Tonikiller10000/8BitProcessor/ClkPulseGenerator/ComputerClk_Pictures/20220915_213736.jpg

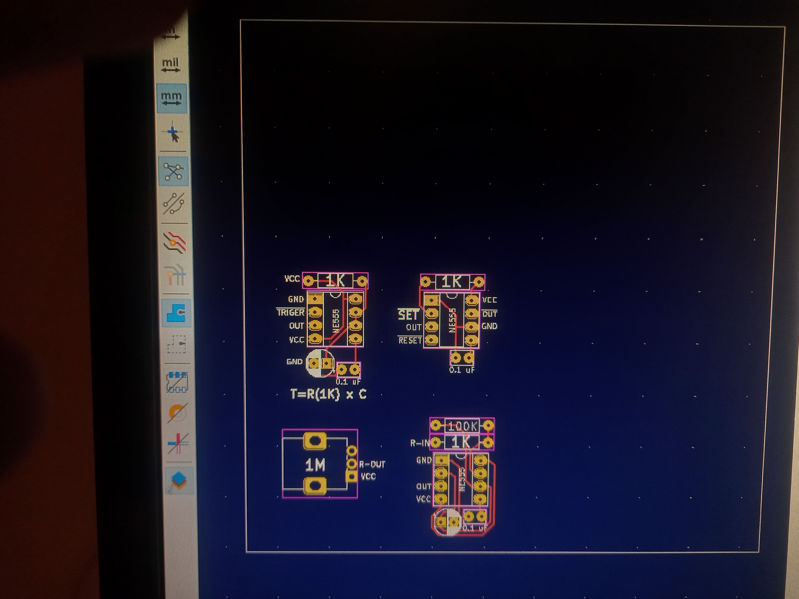
ClkPulseGenerator/ComputerClk_Pictures/20220915_213736.jpg
