Tonikiller10000/8BitProcessor/ClkPulseGenerator/ComputerClk_Pictures/20221016_185711.jpg

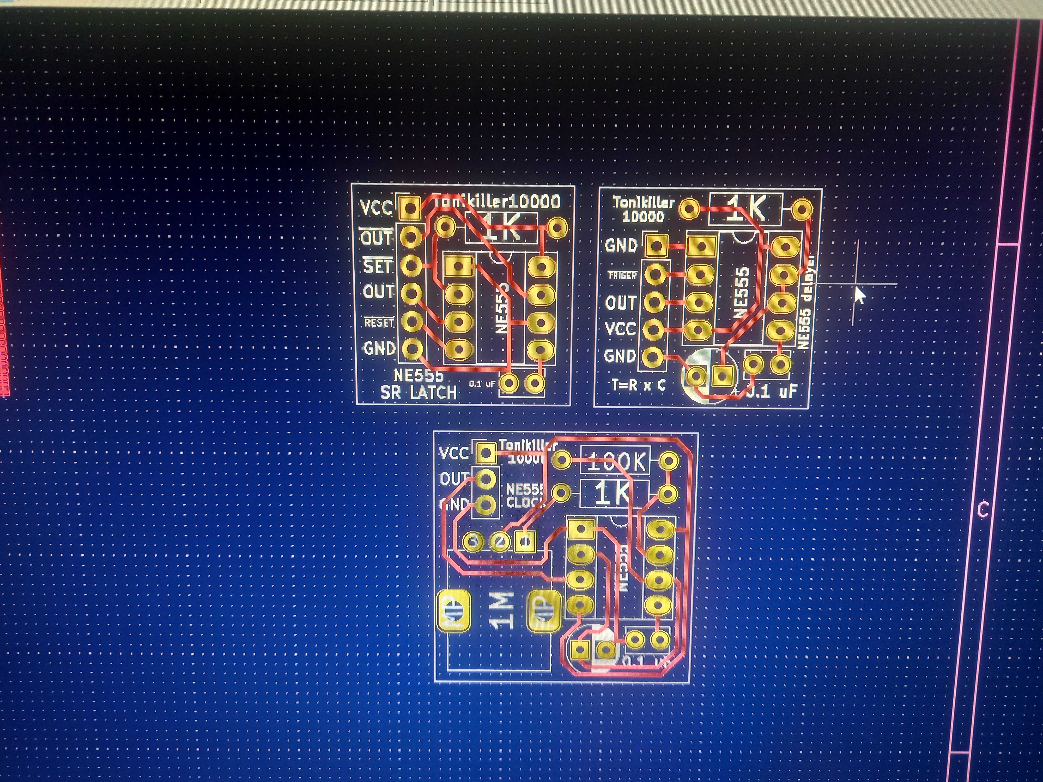
ClkPulseGenerator/ComputerClk_Pictures/20221016_185711.jpg
