Tonikiller10000/8BitProcessor/ClkPulseGenerator/ComputerClk_Pictures/20221231_235716.jpg

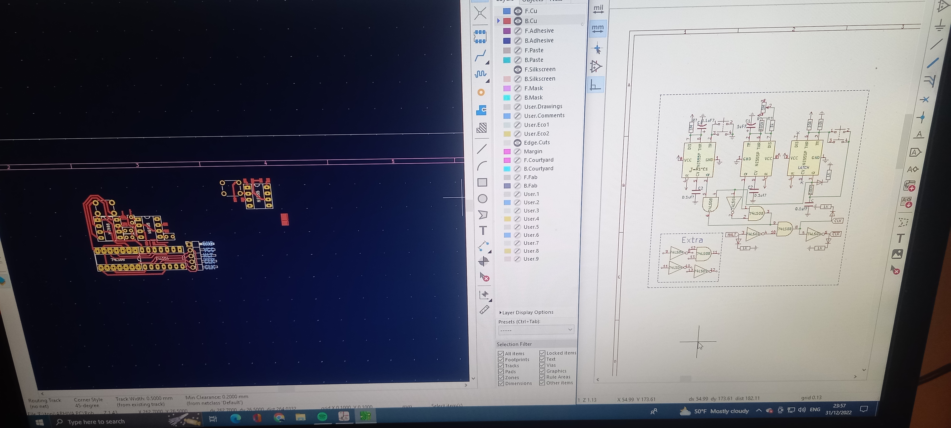
ClkPulseGenerator/ComputerClk_Pictures/20221231_235716.jpg
