Tonikiller10000/8BitProcessor/ClkPulseGenerator/ComputerClk_Pictures/20230512_194840.jpg

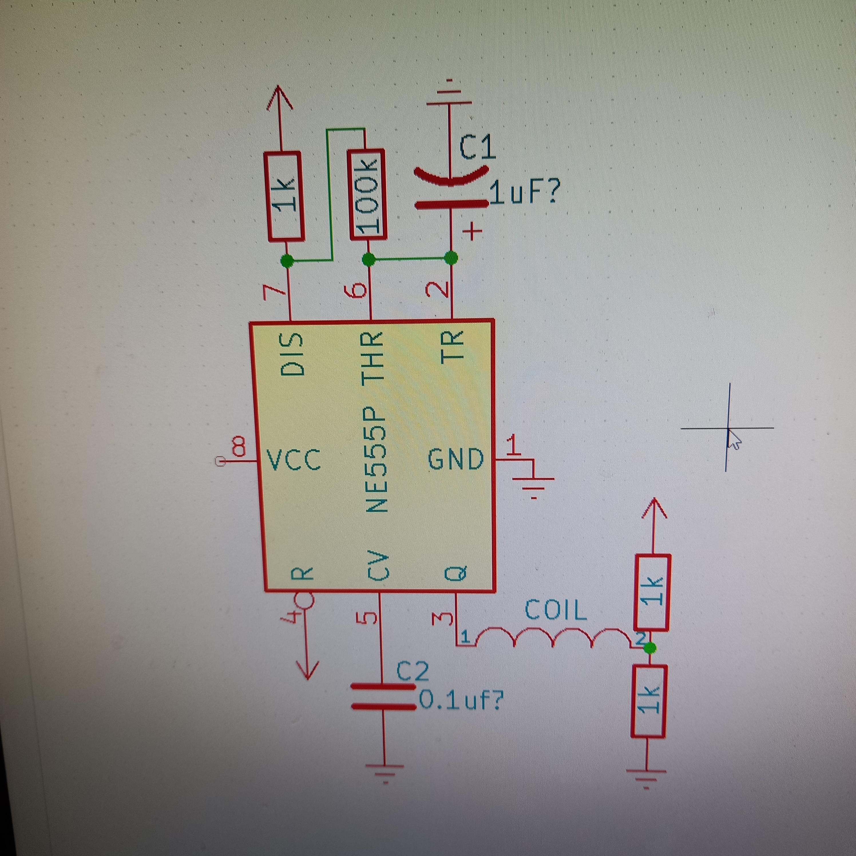
ClkPulseGenerator/ComputerClk_Pictures/20230512_194840.jpg
