Tonikiller10000/8BitProcessor/ClkPulseGenerator/ComputerClk_Pictures/20230818_153651.jpg

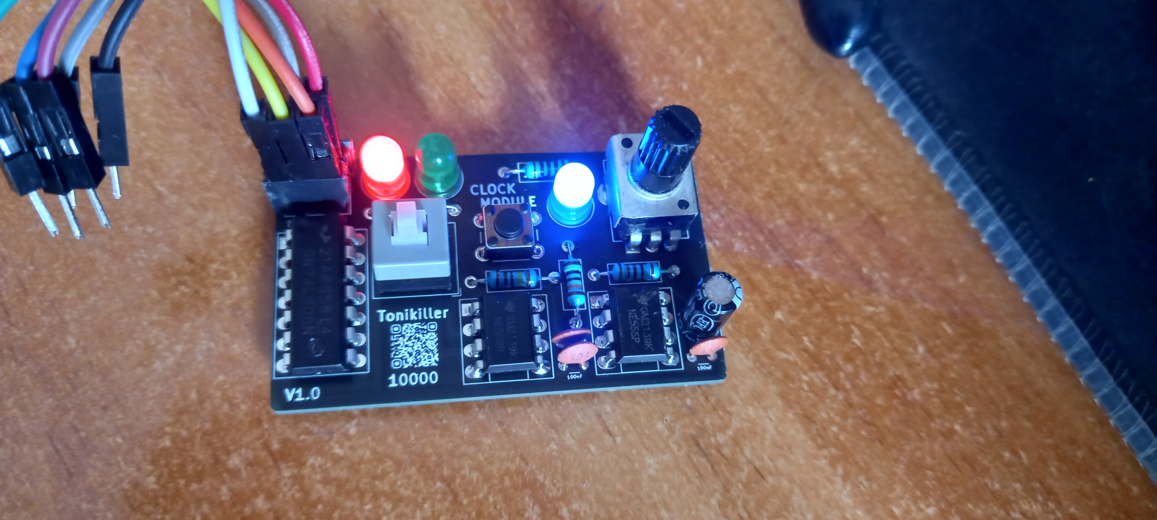
ClkPulseGenerator/ComputerClk_Pictures/20230818_153651.jpg
