Tonikiller10000/8BitProcessor/ClkPulseGenerator/ComputerClk_Pictures/p1.jpg

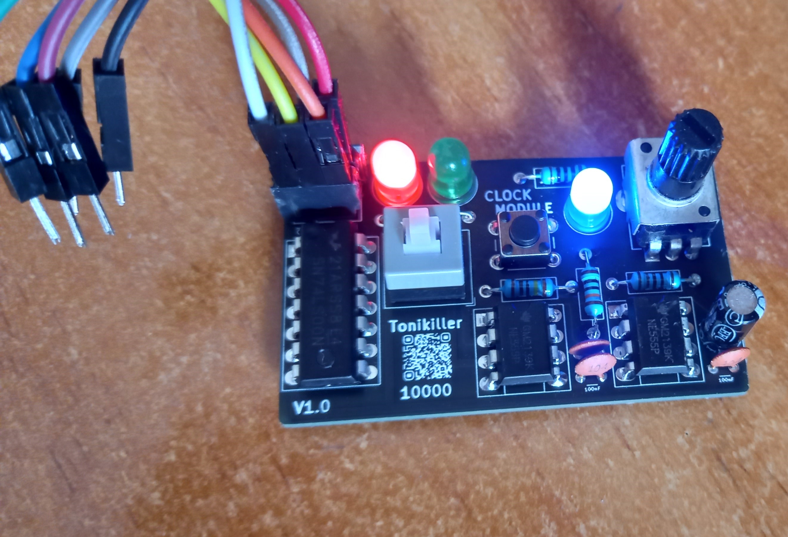
ClkPulseGenerator/ComputerClk_Pictures/p1.jpg
