Tonikiller10000/8BitProcessor/ClkPulseGenerator/ComputerClk_Pictures/p2.jpg

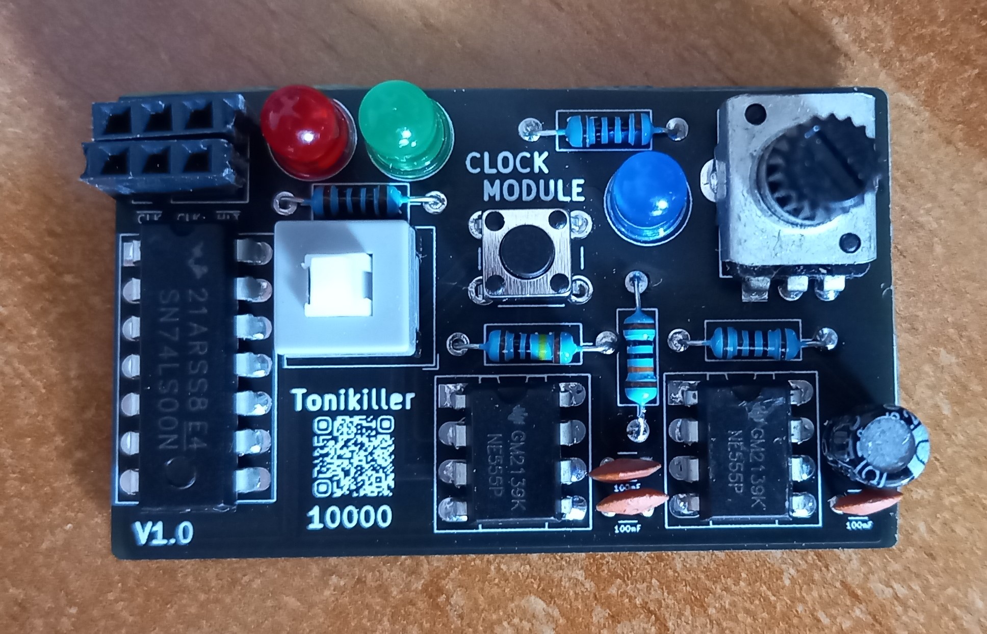
ClkPulseGenerator/ComputerClk_Pictures/p2.jpg
