Tonikiller10000/8BitProcessor/ClkPulseGenerator/ComputerClk_Pictures/s1.png

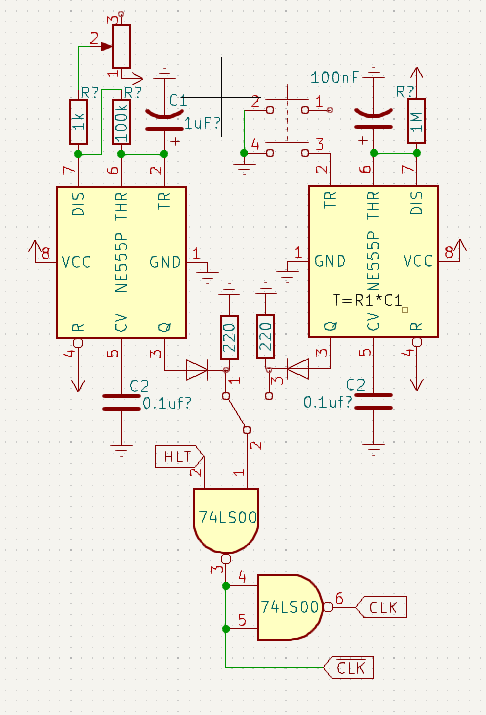
ClkPulseGenerator/ComputerClk_Pictures/s1.png
