Tonikiller10000/8BitProcessor/ClkPulseGenerator/ComputerClk_Pictures/s2.png

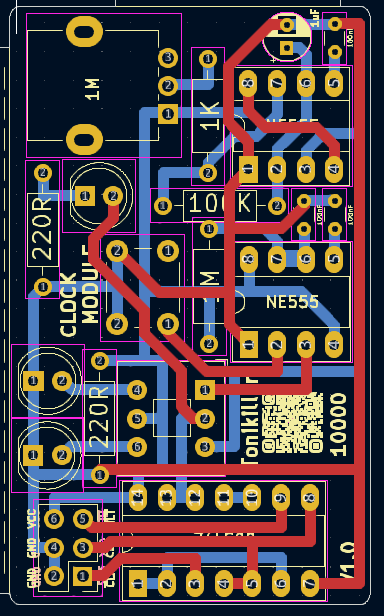
ClkPulseGenerator/ComputerClk_Pictures/s2.png
