Tonikiller10000/8BitProcessor/ClkPulseGenerator/ComputerClk_Pictures/s3.png

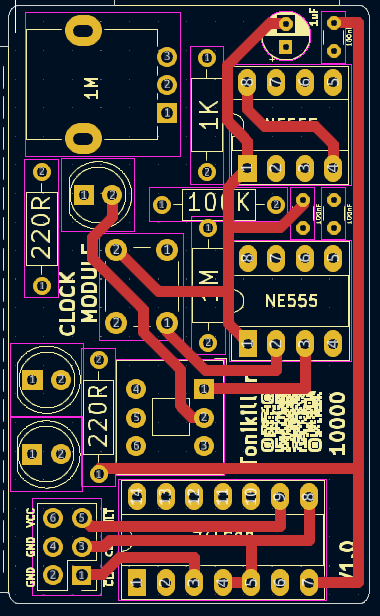
ClkPulseGenerator/ComputerClk_Pictures/s3.png
