Tonikiller10000/8BitProcessor/ClkPulseGenerator/ComputerClk_Pictures/Screenshot 2023-10-15 125649.png

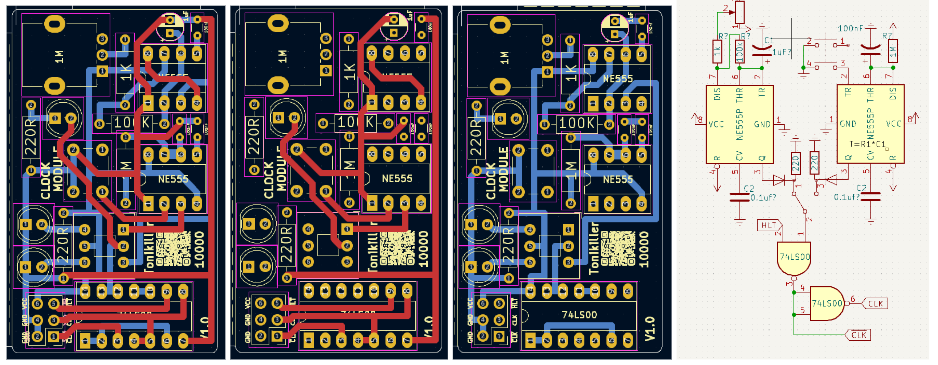
ClkPulseGenerator/ComputerClk_Pictures/Screenshot 2023-10-15 125649.png
