Tonikiller10000/8BitProcessor/ClkPulseGenerator/ComputerClk_Pictures/{35175EC8-5557-4C38-9353-143CC6CB5B68}.png

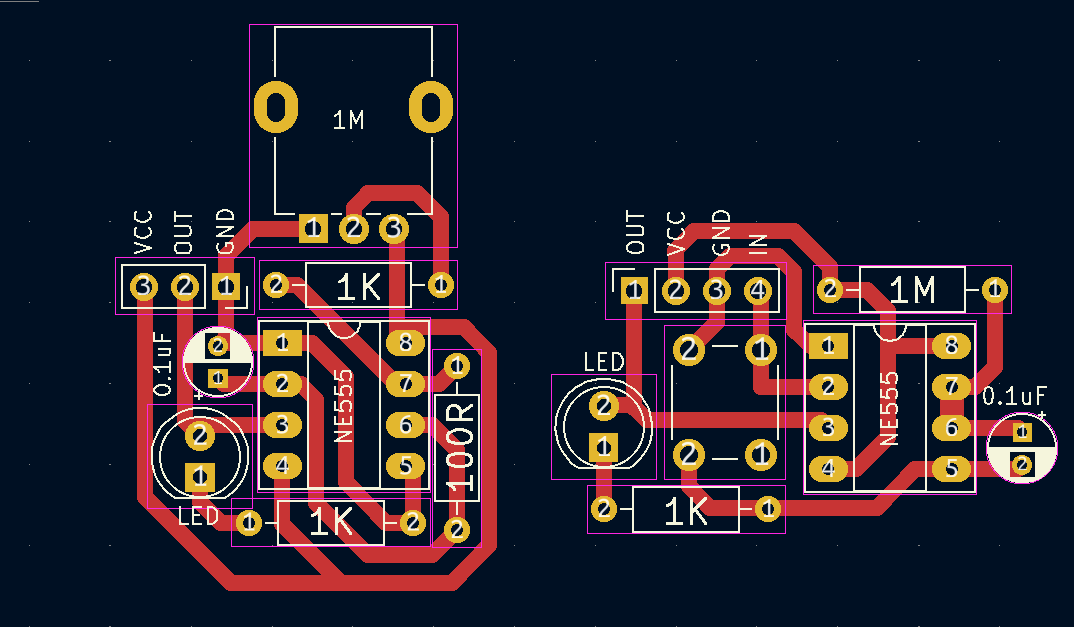
ClkPulseGenerator/ComputerClk_Pictures/{35175EC8-5557-4C38-9353-143CC6CB5B68}.png
