Tonikiller10000/8BitProcessor/DisplayRegister/DisplayRegister_Pictures/DisplayRegisterPicture (1).jpg

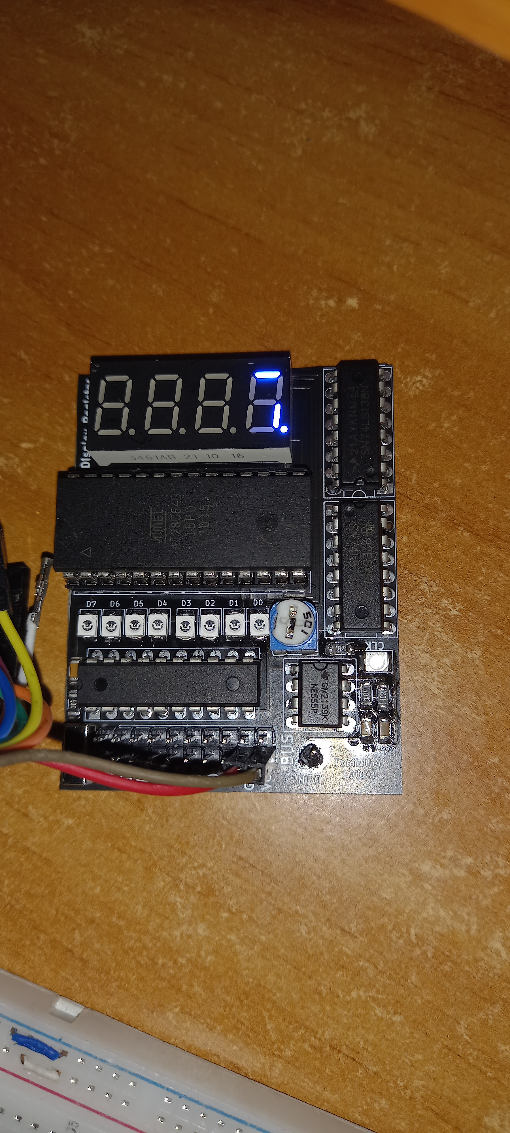
DisplayRegister/DisplayRegister_Pictures/DisplayRegisterPicture (1).jpg
