Tonikiller10000/8BitProcessor/DisplayRegister/DisplayRegister_Pictures/DisplayRegisterPicture (2).jpg

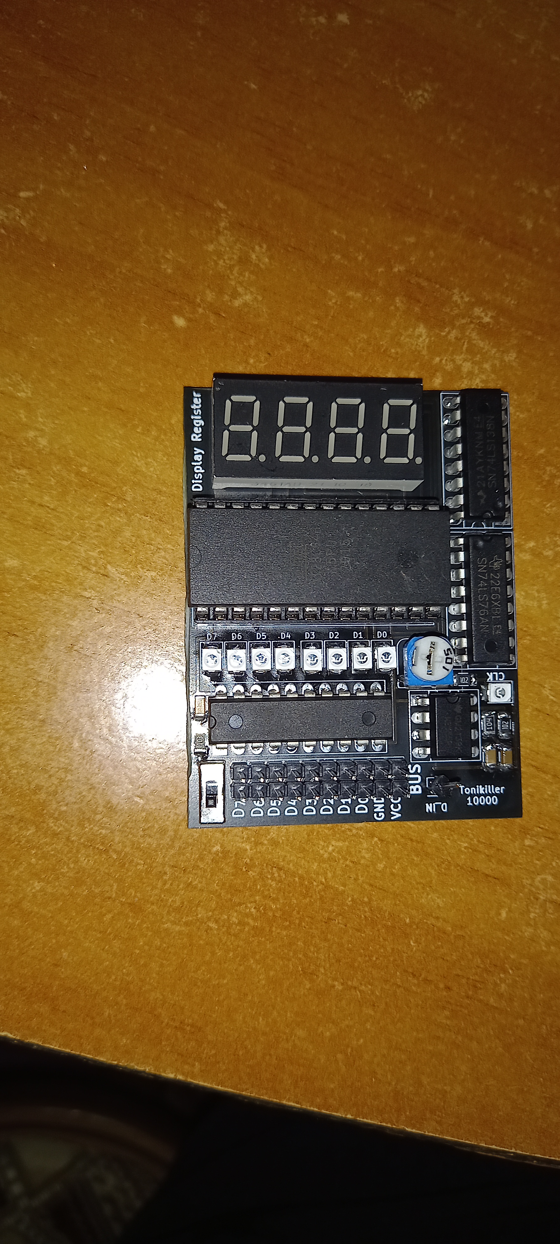
DisplayRegister/DisplayRegister_Pictures/DisplayRegisterPicture (2).jpg
