Tonikiller10000/8BitProcessor/DisplayRegister/DisplayRegister_Pictures/DisplayRegisterPicture (5).jpg

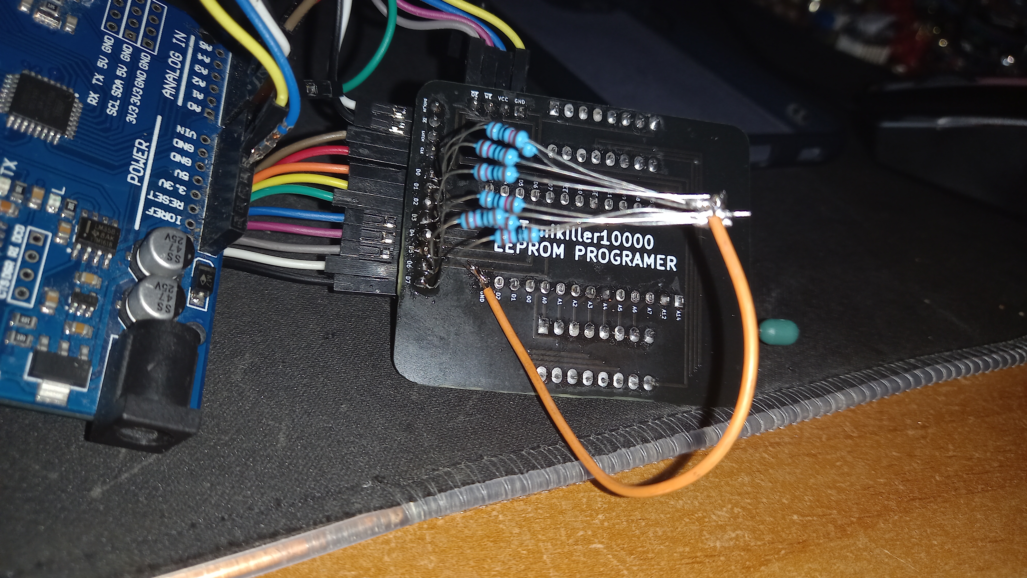
DisplayRegister/DisplayRegister_Pictures/DisplayRegisterPicture (5).jpg
