Tonikiller10000/8BitProcessor/DisplayRegister/DisplayRegister_Pictures/DisplayRegisterPicture (7).png

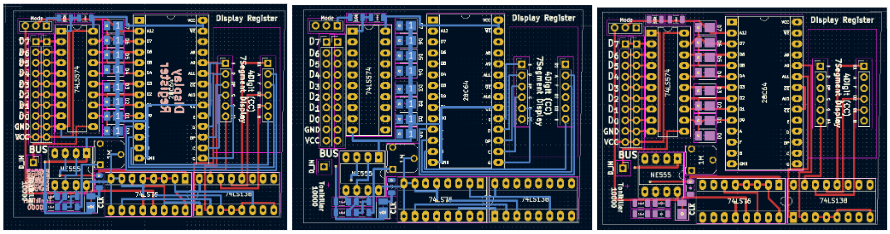
DisplayRegister/DisplayRegister_Pictures/DisplayRegisterPicture (7).png
