Tonikiller10000/8BitProcessor/DisplayRegister/DisplayRegister_Pictures/DisplayRegisterPicture (8).png

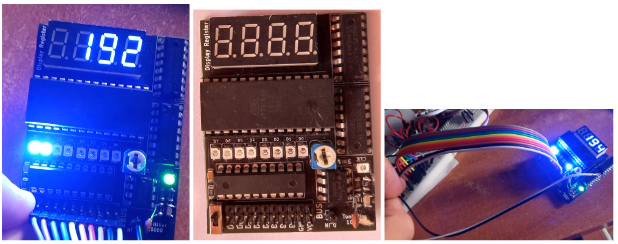
DisplayRegister/DisplayRegister_Pictures/DisplayRegisterPicture (8).png
