Tonikiller10000/8BitProcessor/DisplayRegister/DisplayRegister_Pictures/pic1.jpg

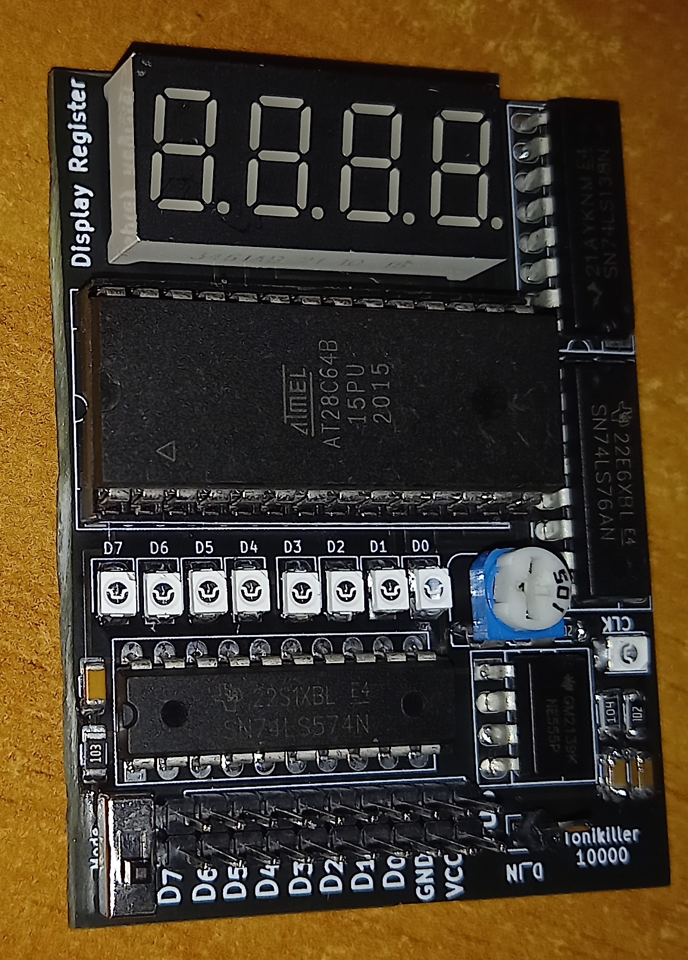
DisplayRegister/DisplayRegister_Pictures/pic1.jpg
