Tonikiller10000/8BitProcessor/DisplayRegister/DisplayRegister_Pictures/pic3.jpg

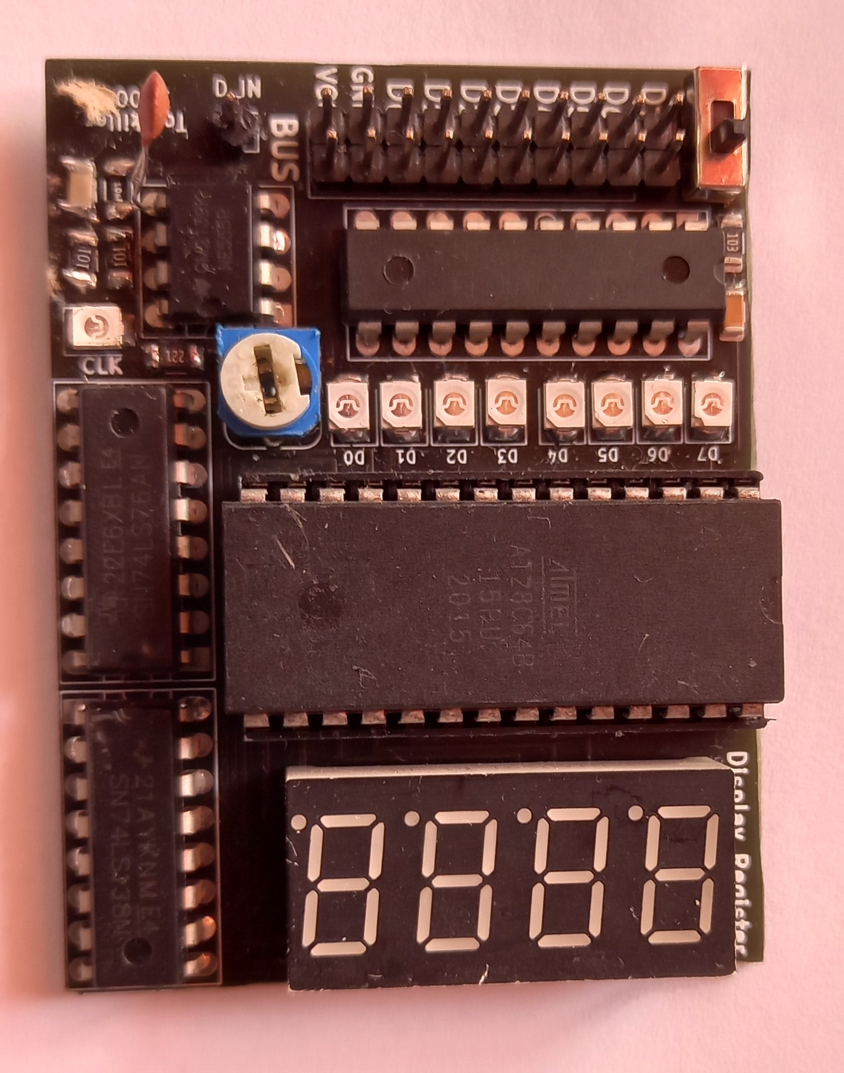
DisplayRegister/DisplayRegister_Pictures/pic3.jpg
