Tonikiller10000/8BitProcessor/DisplayRegister/DisplayRegister_Pictures/pic4.png

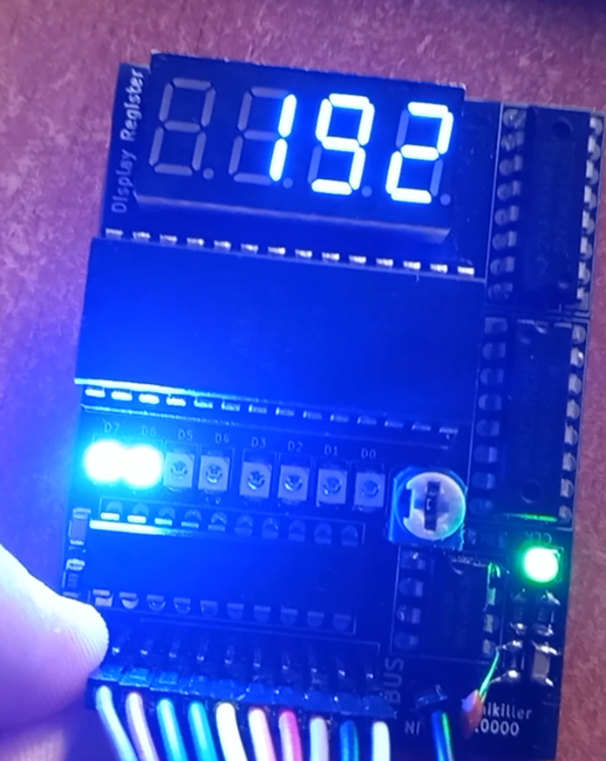
DisplayRegister/DisplayRegister_Pictures/pic4.png
