Tonikiller10000/8BitProcessor/DisplayRegister/DisplayRegister_Pictures/pr1.png

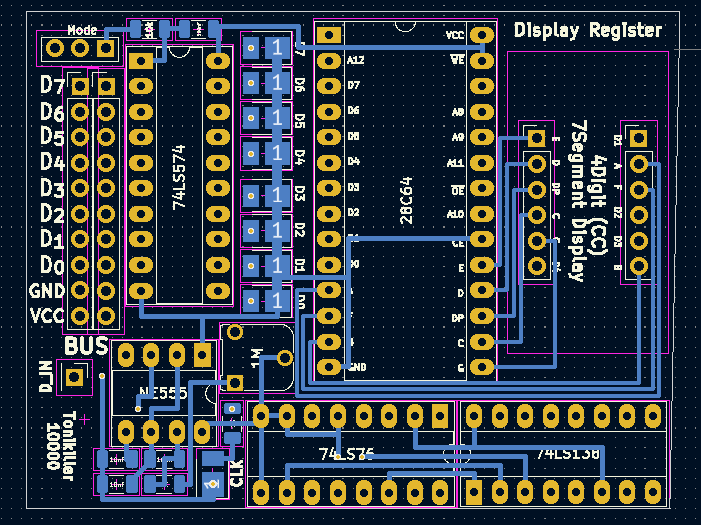
DisplayRegister/DisplayRegister_Pictures/pr1.png
