Tonikiller10000/8BitProcessor/DisplayRegister/DisplayRegister_Pictures/pr2.png

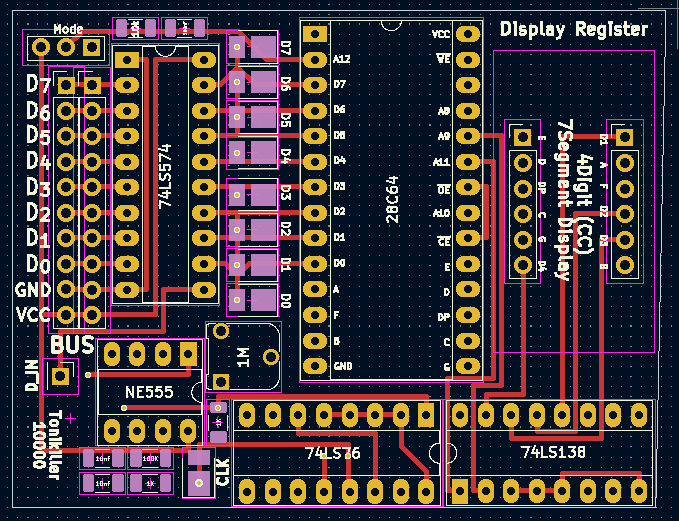
DisplayRegister/DisplayRegister_Pictures/pr2.png
