Tonikiller10000/8BitProcessor/DisplayRegister/DisplayRegister_Pictures/pr3.png

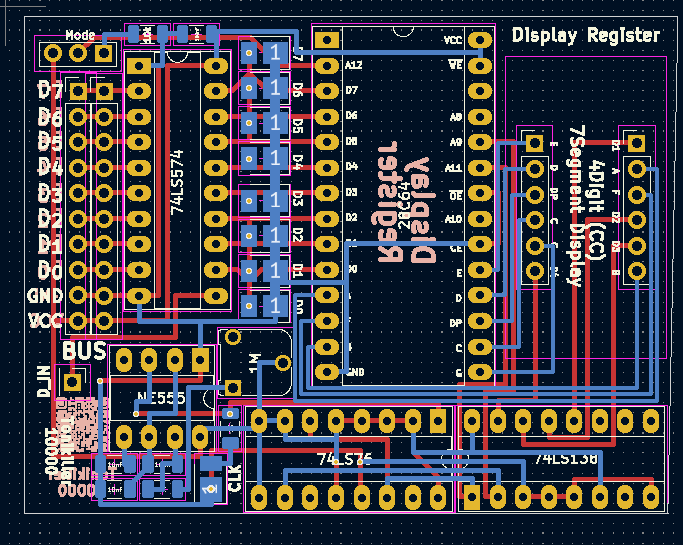
DisplayRegister/DisplayRegister_Pictures/pr3.png
