Tonikiller10000/8BitProcessor/DisplayRegister/DisplayRegister_Pictures/sch.png

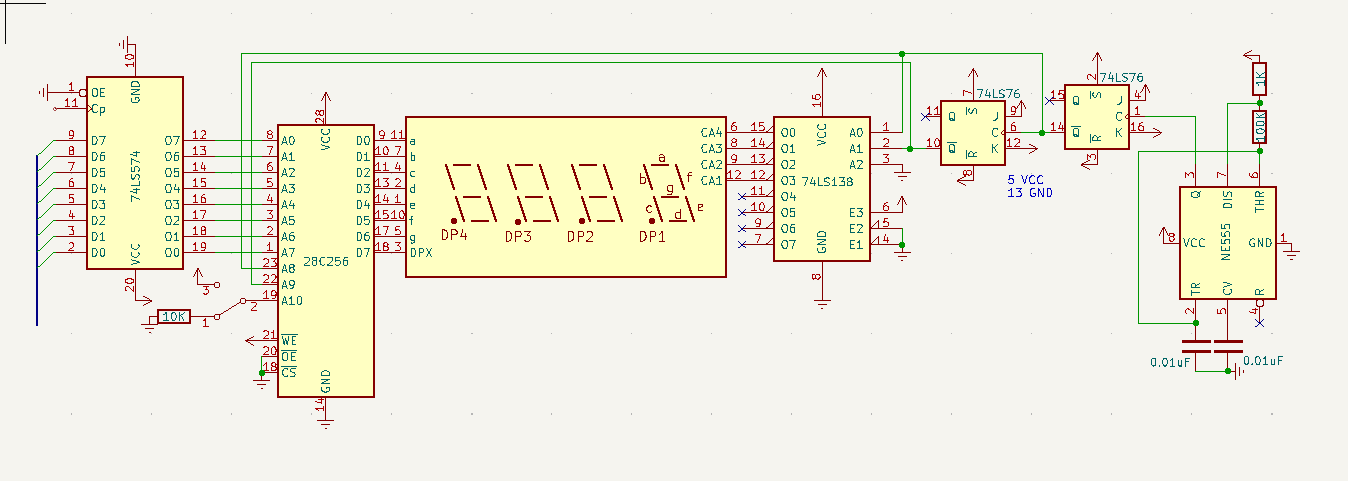
DisplayRegister/DisplayRegister_Pictures/sch.png
