Tonikiller10000/8BitProcessor/Processor_ALU_V1.0/ALU-Pictures/ALU_Picture (1).png

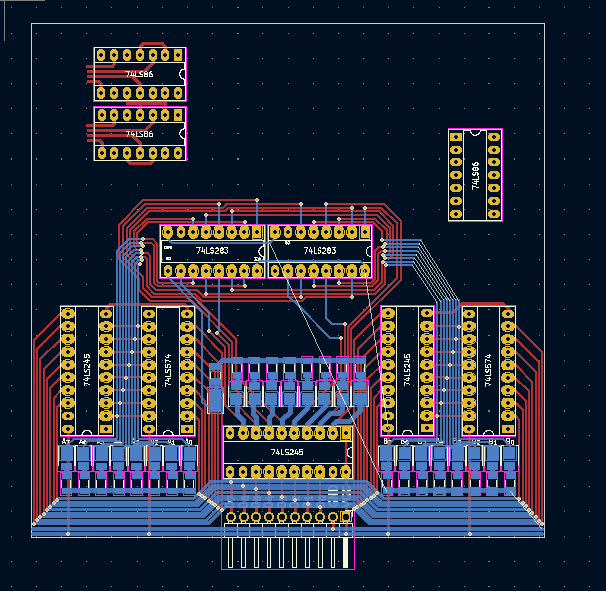
Processor_ALU_V1.0/ALU-Pictures/ALU_Picture (1).png
