Tonikiller10000/8BitProcessor/Processor_ALU_V1.0/ALU-Pictures/ALU_Picture (10).jpg

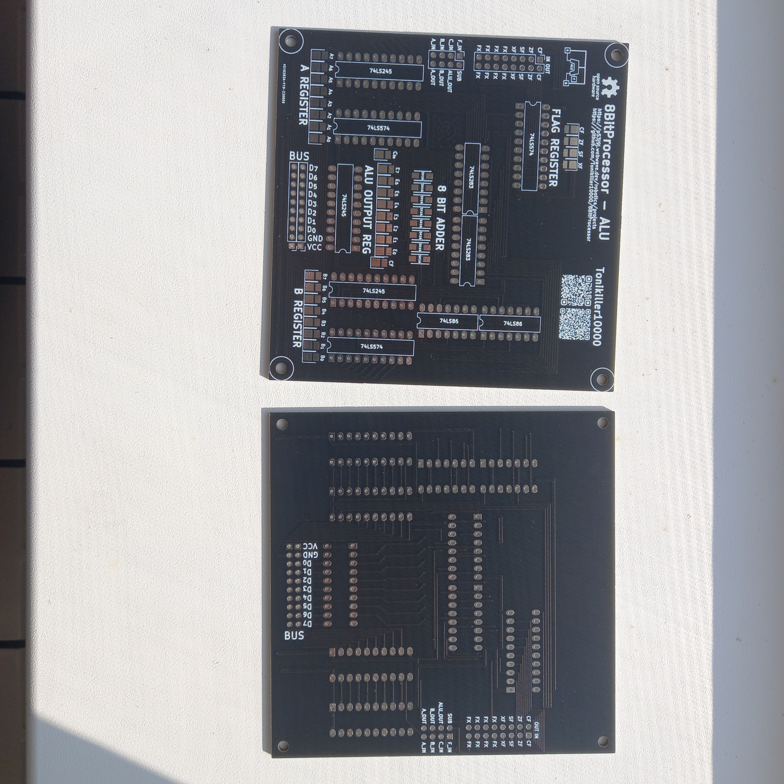
Processor_ALU_V1.0/ALU-Pictures/ALU_Picture (10).jpg
