Tonikiller10000/8BitProcessor/ProcessorPhotos/{8CCBF4A2-A508-434C-9C56-49CF454CE7C5}.png

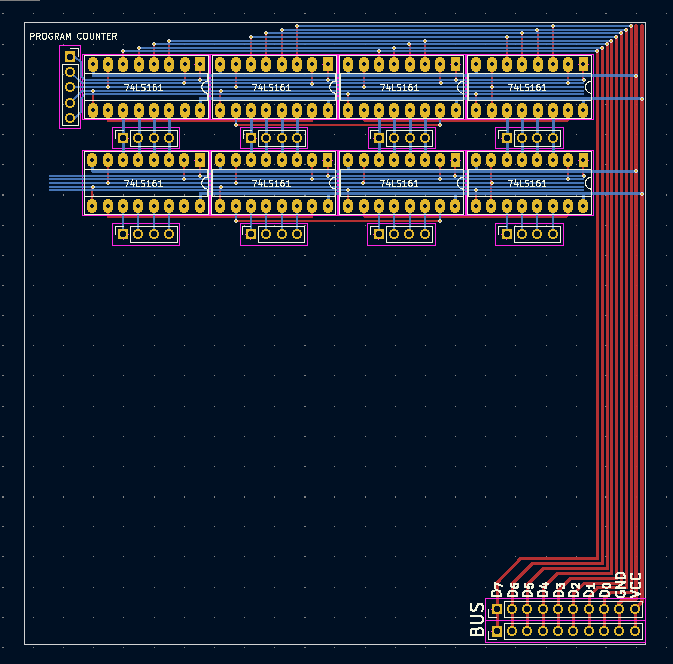
ProcessorPhotos/{8CCBF4A2-A508-434C-9C56-49CF454CE7C5}.png
