Tonikiller10000/8BitProcessor/ProcessorPhotos/{50643307-304F-4F32-9E74-329941639F6F}.png

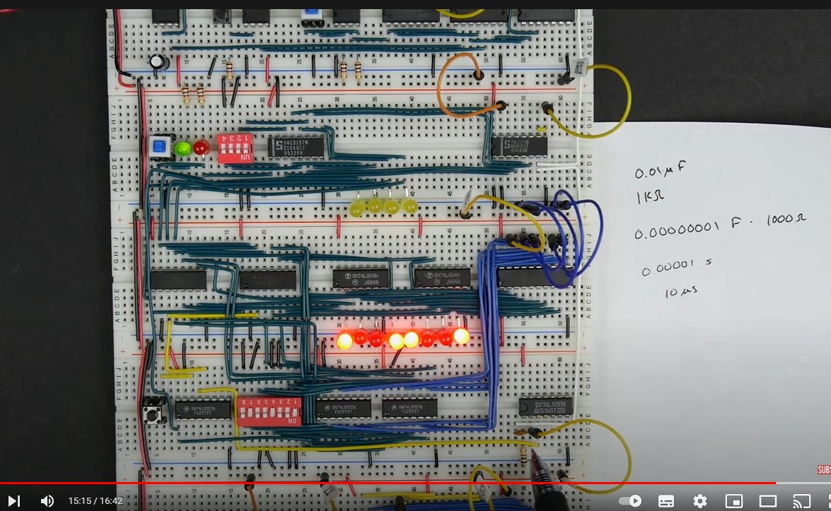
ProcessorPhotos/{50643307-304F-4F32-9E74-329941639F6F}.png
