Tonikiller10000/8BitProcessor/Processor_ALU_V1.0/Processor-ALU/Processor-ALU.kicad_sch

## KiCad design Processor_ALU_V1.0/Processor-ALU/Processor-ALU.kicad_sch (2023-09-09)

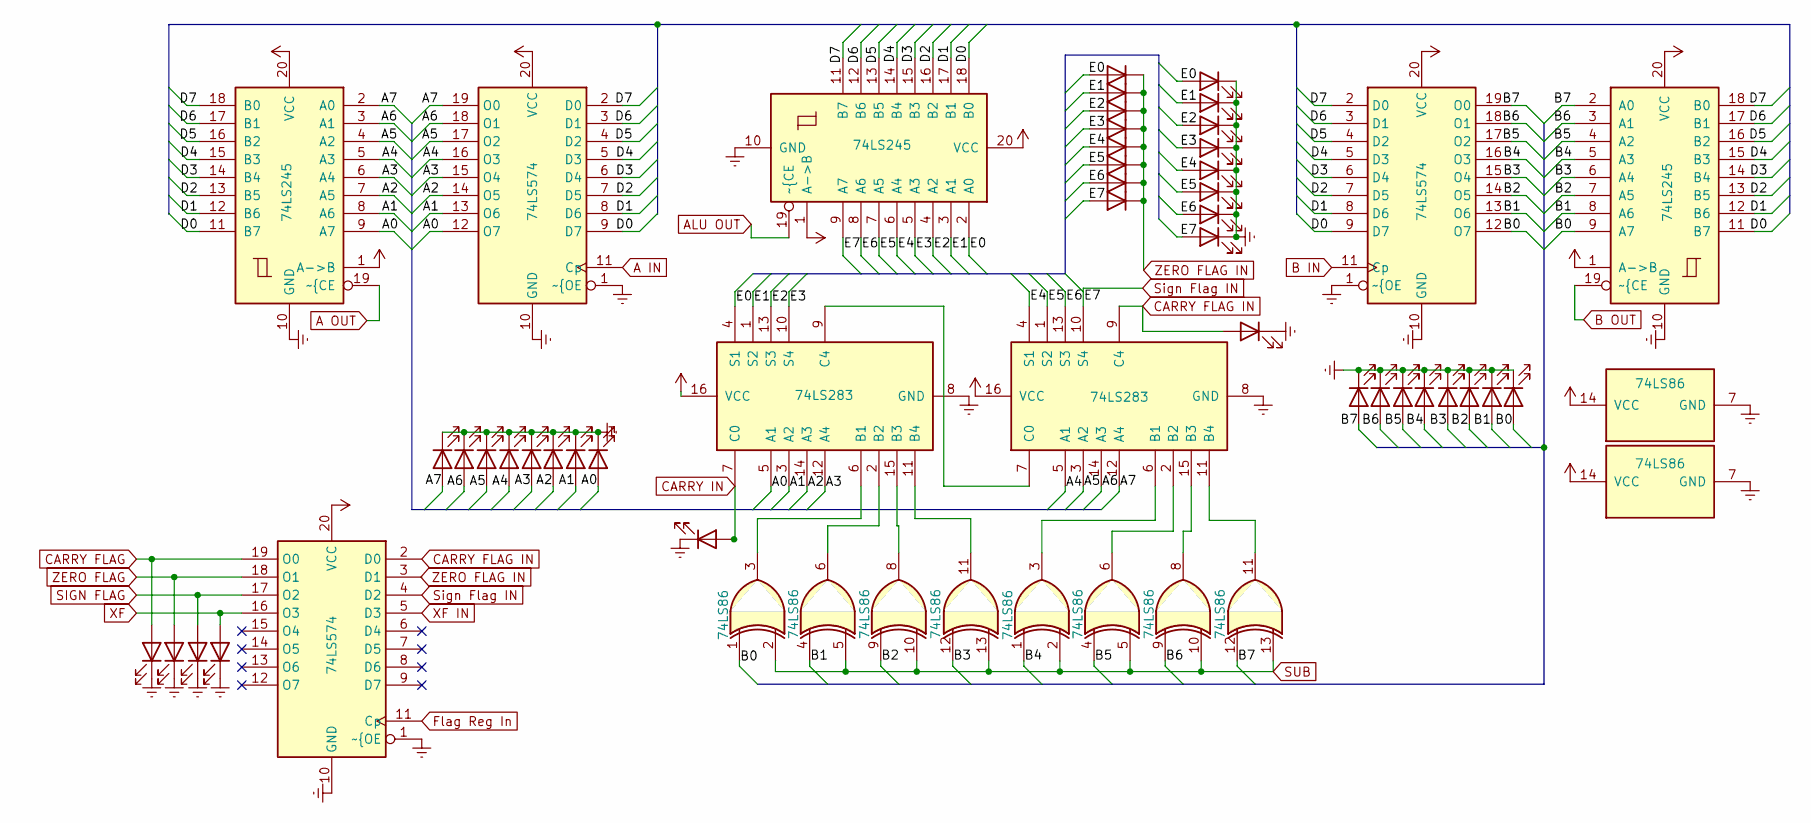
[picture p59: schematic Processor-ALU.kicad_sch]

Parts:
D1: C_{in}; LED_PLCC_2835
D2: XF; LED_PLCC_2835
D3: SF; LED_PLCC_2835
D4: ZF; LED_PLCC_2835
D5: CF; LED_PLCC_2835
D6, D10, D11, D12, D13, D14, D15, D17, D18, D34, D35, D36, D37, D38, D39, D40, D41, D42, D43, D44, D45, D46, D47, D48, D49: LED; LED_PLCC_2835
D16, D27, D28, D29, D30, D31, D32, D33: SK16; DIOM5027X250N
U1, U6, U10: 74LS245; DIP-20_W7.62mm_LongPads
U2, U3, U9: 74LS574; DIP-20_W7.62mm_LongPads
U4, U7: 74LS86; DIP-14_W7.62mm_LongPads
U5, U8: 74LS283; DIP-16_W7.62mm_LongPads

Connections:
A0: D18.2 (A), U1.9 (A7), U3.12 (O7), U5.5 (A1)
A1: D17.2 (A), U1.8 (A6), U3.13 (O6), U5.3 (A2)
A2: D15.2 (A), U1.7 (A5), U3.14 (O5), U5.14 (A3)
A3: D14.2 (A), U1.6 (A4), U3.15 (O4), U5.12 (A4)
A4: D13.2 (A), U1.5 (A3), U3.16 (O3), U8.5 (A1)
A5: D12.2 (A), U1.4 (A2), U3.17 (O2), U8.3 (A2)
A6: D11.2 (A), U1.3 (A1), U3.18 (O1), U8.14 (A3)
A7: D10.2 (A), U1.2 (A0), U3.19 (O0), U8.12 (A4)
A IN: U3.11 (Cp)
A OUT: U1.19 (~{CE)
ALU OUT: U6.19 (~{CE)
B0: D49.2 (A), U4.1, U9.12 (O7), U10.9 (A7)
B1: D48.2 (A), U4.4, U9.13 (O6), U10.8 (A6)
B2: D47.2 (A), U4.9, U9.14 (O5), U10.7 (A5)
B3: D46.2 (A), U4.12, U9.15 (O4), U10.6 (A4)
B4: D45.2 (A), U7.1, U9.16 (O3), U10.5 (A3)
B5: D44.2 (A), U7.4, U9.17 (O2), U10.4 (A2)
B6: D43.2 (A), U7.9, U9.18 (O1), U10.3 (A1)
B7: D42.2 (A), U7.12, U9.19 (O0), U10.2 (A0)
B IN: U9.11 (Cp)
B OUT: U10.19 (~{CE)
CARRY FLAG: D2.2 (A), U2.19 (O0)
CARRY FLAG IN: D6.2 (A), U2.2 (D0), U8.9 (C4)
CARRY IN: D1.2 (A), U5.7 (C0)
D0: U1.11 (B7), U3.9 (D7), U6.18 (B0), U9.9 (D7), U10.11 (B7)
D1: U1.12 (B6), U3.8 (D6), U6.17 (B1), U9.8 (D6), U10.12 (B6)
D2: U1.13 (B5), U3.7 (D5), U6.16 (B2), U9.7 (D5), U10.13 (B5)
D3: U1.14 (B4), U3.6 (D4), U6.15 (B3), U9.6 (D4), U10.14 (B4)
D4: U1.15 (B3), U3.5 (D3), U6.14 (B4), U9.5 (D3), U10.15 (B3)
D5: U1.16 (B2), U3.4 (D2), U6.13 (B5), U9.4 (D2), U10.16 (B2)
D6: U1.17 (B1), U3.3 (D1), U6.12 (B6), U9.3 (D1), U10.17 (B1)
D7: U1.18 (B0), U3.2 (D0), U6.11 (B7), U9.2 (D0), U10.18 (B0)
E0: D27.1 (A), D34.2 (A), U5.4 (S1), U6.2 (A0)
E1: D28.1 (A), D35.2 (A), U5.1 (S2), U6.3 (A1)
E2: D29.1 (A), D36.2 (A), U5.13 (S3), U6.4 (A2)
E3: D30.1 (A), D37.2 (A), U5.10 (S4), U6.5 (A3)
E4: D31.1 (A), D38.2 (A), U6.6 (A4), U8.4 (S1)
E5: D32.1 (A), D39.2 (A), U6.7 (A5), U8.1 (S2)
E6: D33.1 (A), D40.2 (A), U6.8 (A6), U8.13 (S3)
Earth: D1.1 (K), D2.1 (K), D3.1 (K), D4.1 (K), D5.1 (K), D6.1 (K), D10.1 (K), D11.1 (K), D12.1 (K), D13.1 (K), D14.1 (K), D15.1 (K), D17.1 (K), D18.1 (K), D34.1 (K), D35.1 (K), D36.1 (K), D37.1 (K), D38.1 (K), D39.1 (K), D40.1 (K), D41.1 (K), D42.1 (K), D43.1 (K), D44.1 (K), D45.1 (K), D46.1 (K), D47.1 (K), D48.1 (K), D49.1 (K), U1.10 (GND), U2.1 (~{OE), U2.10 (GND), U3.1 (~{OE), U3.10 (GND), U4.7 (GND), U5.8 (GND), U6.10 (GND), U7.7 (GND), U8.8 (GND), U9.1 (~{OE), U9.10 (GND), U10.10 (GND)
Flag Reg In: U2.11 (Cp)
unnamed: U4.3, U5.6 (B1)
unnamed: U4.6, U5.2 (B2)
unnamed: U4.8, U5.15 (B3)
unnamed: U4.11, U5.11 (B4)
unnamed: U5.9 (C4), U8.7 (C0)
unnamed: U7.3, U8.6 (B1)
unnamed: U7.6, U8.2 (B2)
unnamed: U7.8, U8.15 (B3)
unnamed: U7.11, U8.11 (B4)
SIGN FLAG: D4.2 (A), U2.17 (O2)
SUB: U4.2, U4.5, U4.10, U4.13, U7.2, U7.5, U7.10, U7.13
Sign Flag IN: D16.1 (A), D41.2 (A), U2.4 (D2), U6.9 (A7), U8.10 (S4)
VCC: U1.1 (A->B), U1.20 (VCC), U2.20 (VCC), U3.20 (VCC), U4.14 (VCC), U5.16 (VCC), U6.1 (A->B), U6.20 (VCC), U7.14 (VCC), U8.16 (VCC), U9.20 (VCC), U10.1 (A->B), U10.20 (VCC)
XF: D5.2 (A), U2.16 (O3)
XF IN: U2.5 (D3)
ZERO FLAG: D3.2 (A), U2.18 (O1)
ZERO FLAG IN: D16.2 (K), D27.2 (K), D28.2 (K), D29.2 (K), D30.2 (K), D31.2 (K), D32.2 (K), D33.2 (K), U2.3 (D1)
